CRMHosting/CheeseMakingBath/docs/images/2020-11-29_17-01-23.png

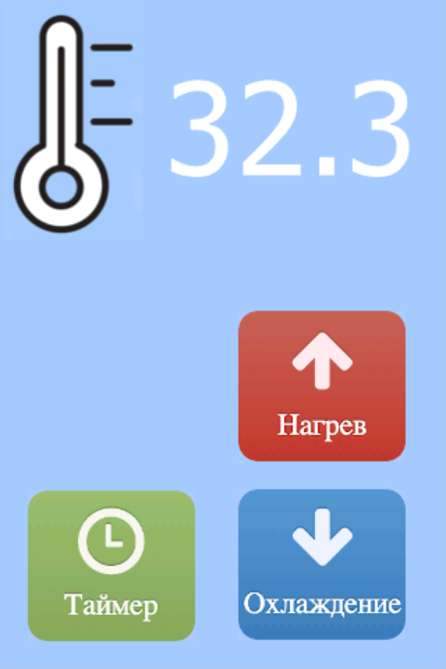
docs/images/2020-11-29_17-01-23.png
