CRMHosting/CheeseMakingBath/docs/images/2020-11-29_17-01-56.png

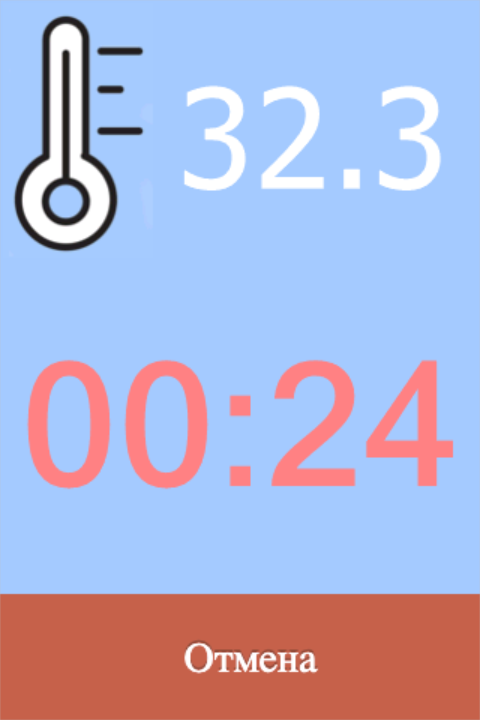
docs/images/2020-11-29_17-01-56.png
