CRMHosting/CheeseMakingBath/docs/images/2020-11-29_17-02-31.png

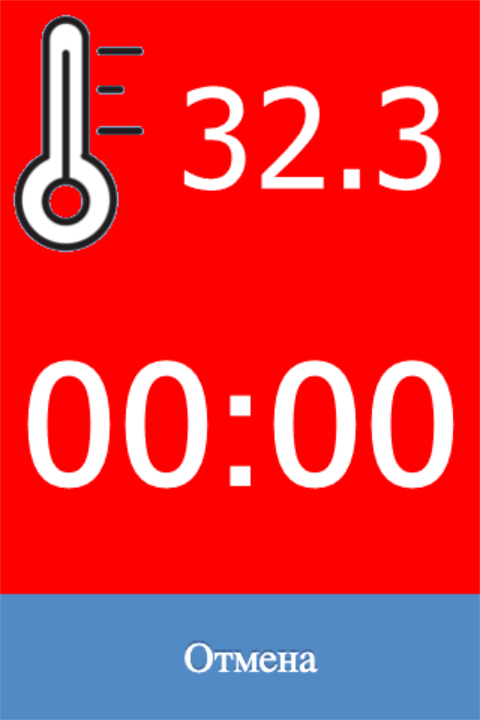
docs/images/2020-11-29_17-02-31.png
