CRMHosting/CheeseMakingBath/docs/images/2020-11-29_17-03-14.png

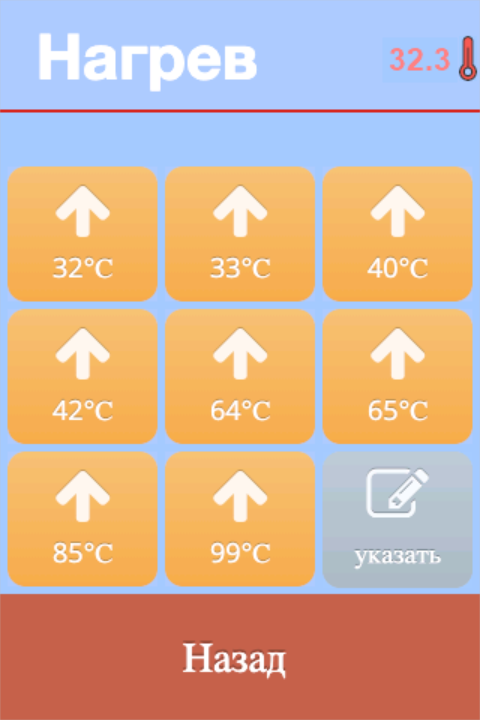
docs/images/2020-11-29_17-03-14.png
