CRMHosting/CheeseMakingBath/docs/images/2020-11-29_17-03-38.png

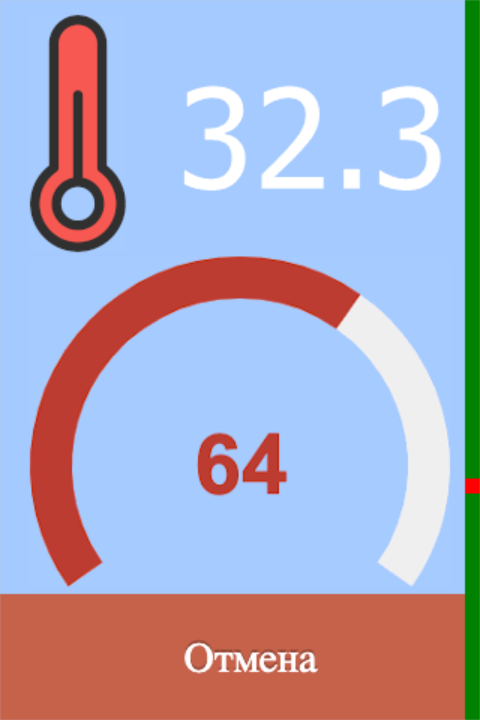
docs/images/2020-11-29_17-03-38.png
