CRMHosting/CheeseMakingBath/docs/images/2020-11-29_17-04-29.png

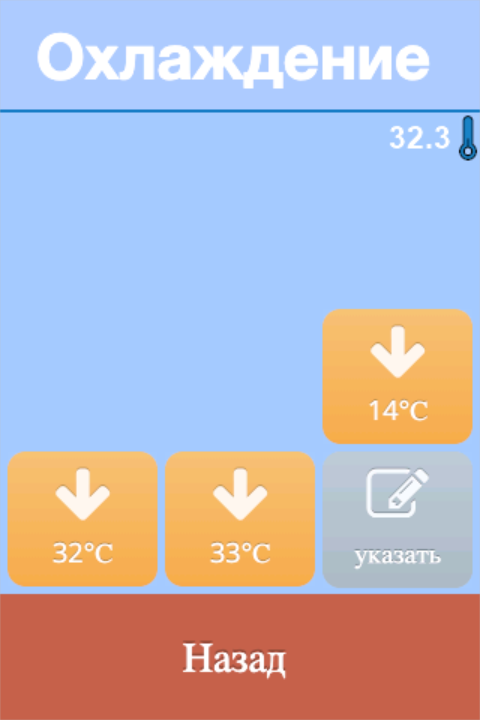
docs/images/2020-11-29_17-04-29.png
