CRMHosting/CheeseMakingBath/docs/images/2020-11-29_17-04-42.png

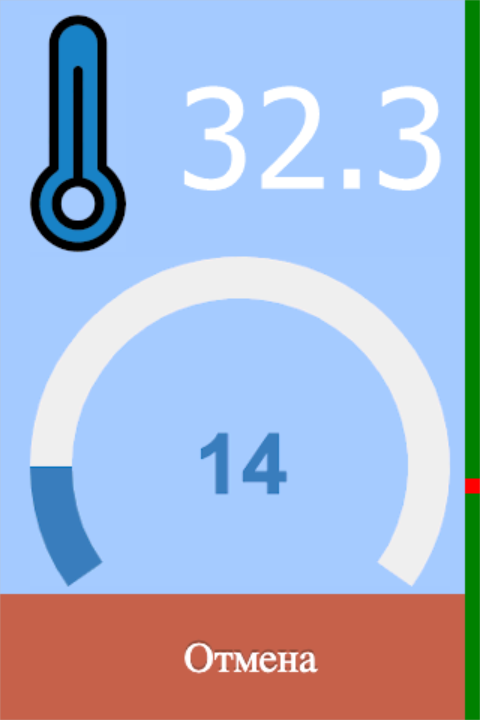
docs/images/2020-11-29_17-04-42.png
