CRMHosting/CheeseMakingBath/docs/images/2020-11-29_17-05-11.png

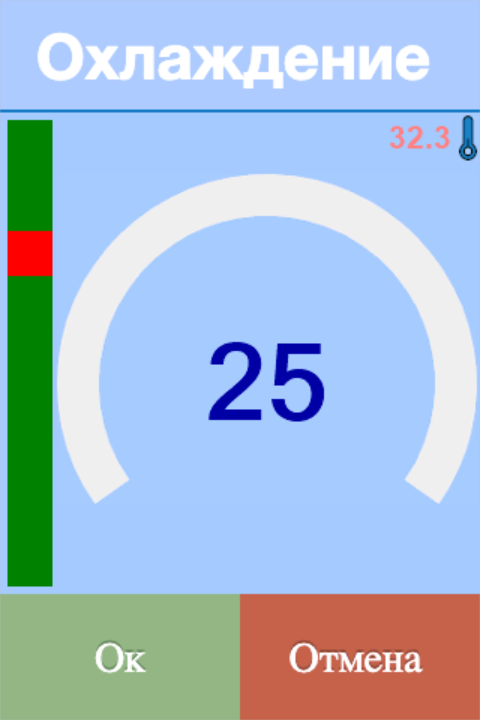
docs/images/2020-11-29_17-05-11.png
