CRMHosting/CheeseMakingBath/docs/images/2020-11-29_19-46-53.png

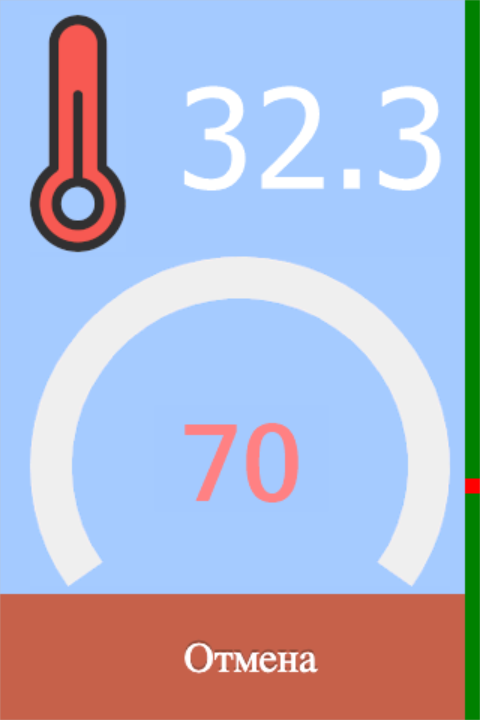
docs/images/2020-11-29_19-46-53.png
