CRMHosting/CheeseMakingBath/docs/images/1606628371465.jpg

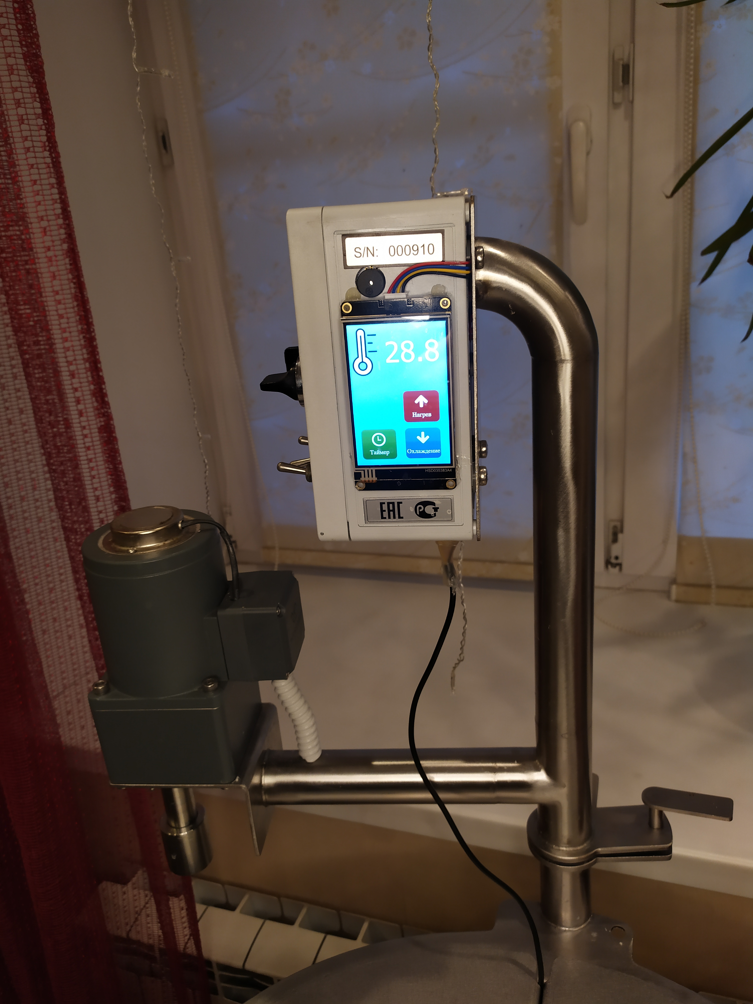
docs/images/1606628371465.jpg
