CRMHosting/CheeseMakingBath/docs/images/1606628371484.jpg

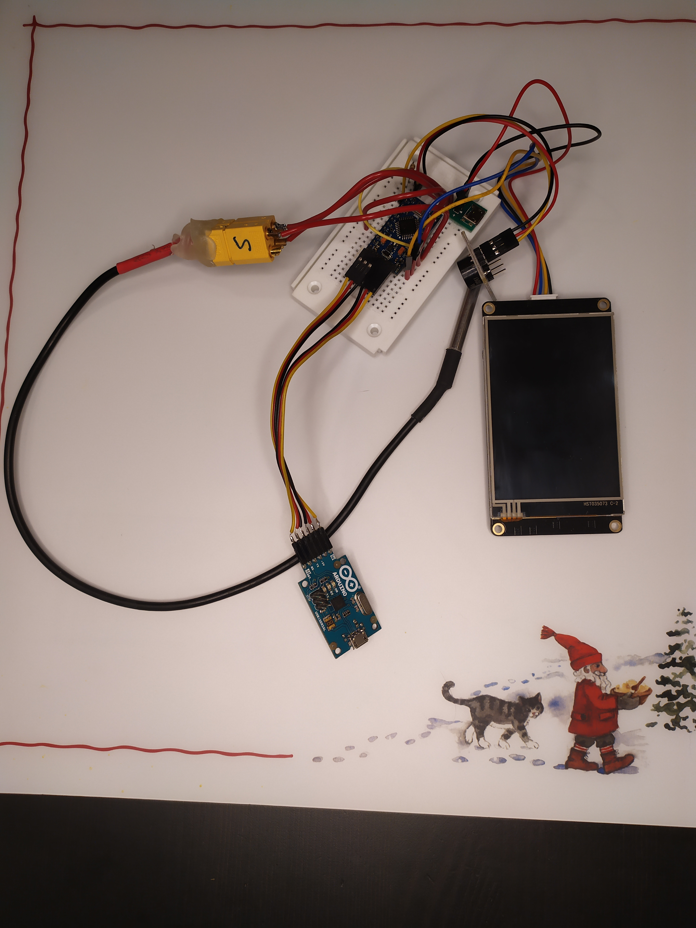
docs/images/1606628371484.jpg
