CRMHosting/CheeseMakingBath/docs/images/main-pH-280x420.png

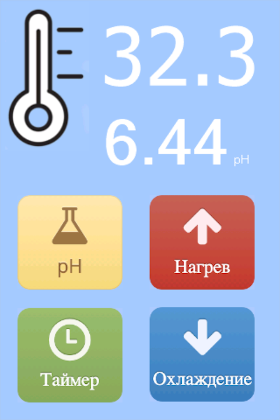
docs/images/main-pH-280x420.png
