CRMHosting/CheeseMakingBath/docs/images/pH-280x420.png

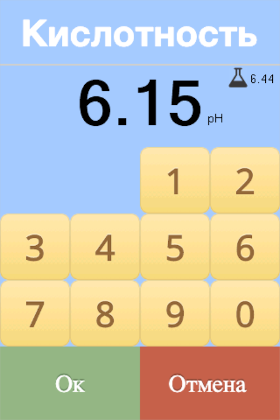
docs/images/pH-280x420.png
