CRMHosting/CheeseMakingBath/docs/images/pH-run-280x420.png

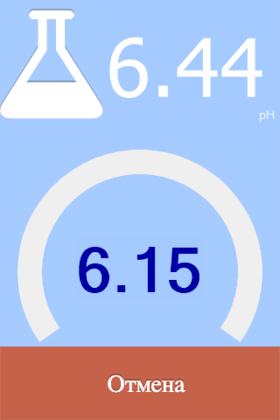
docs/images/pH-run-280x420.png
