CRMHosting/CheeseMakingBath/docs/images/screen-h-full-640x.png

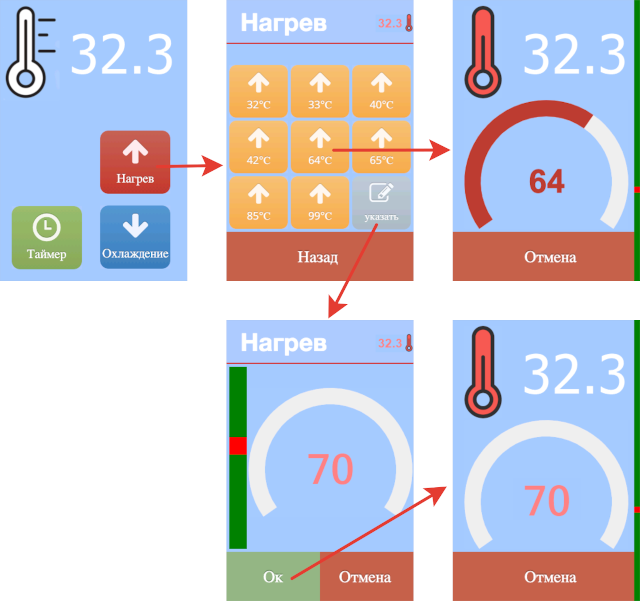
docs/images/screen-h-full-640x.png
