CRMHosting/CheeseMakingBath/docs/images/screen-pH.png

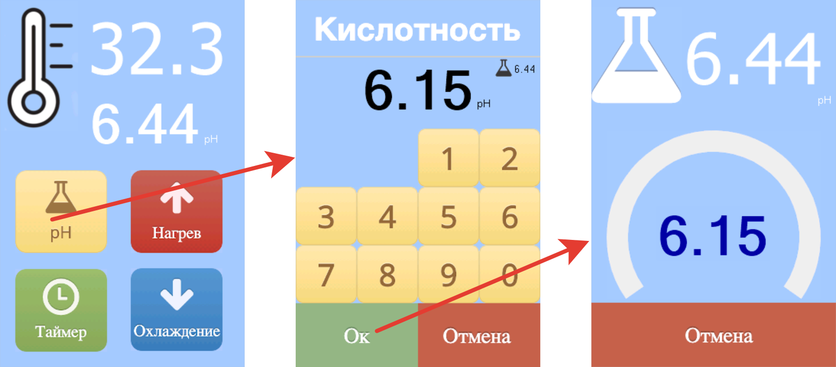
docs/images/screen-pH.png
