CRMHosting/CheeseMakingBath/Nextion/images/buttons/buttons-custom.png

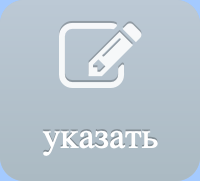
Nextion/images/buttons/buttons-custom.png
