CRMHosting/CheeseMakingBath/Nextion/images/buttons/cooling-buttons-14.png

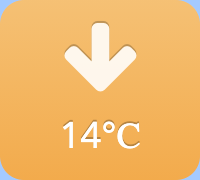
Nextion/images/buttons/cooling-buttons-14.png
