CRMHosting/CheeseMakingBath/Nextion/images/buttons/digital-button-0.png

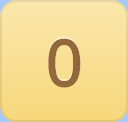
Nextion/images/buttons/digital-button-0.png
