CRMHosting/CheeseMakingBath/Nextion/images/buttons/digital-button-1.png

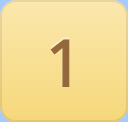
Nextion/images/buttons/digital-button-1.png
