CRMHosting/CheeseMakingBath/Nextion/images/buttons/heat-buttons-40.png

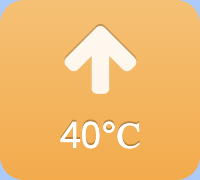
Nextion/images/buttons/heat-buttons-40.png
