CRMHosting/CheeseMakingBath/Nextion/images/buttons/heat-buttons-custom.png

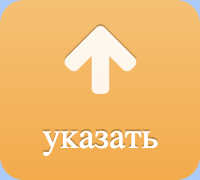
Nextion/images/buttons/heat-buttons-custom.png
