CRMHosting/CheeseMakingBath/Nextion/images/buttons/main-buttons-flocc.png

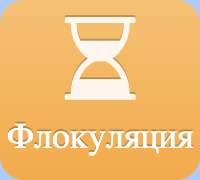
Nextion/images/buttons/main-buttons-flocc.png
