CRMHosting/CheeseMakingBath/Nextion/images/buttons/main-buttons-freese.png

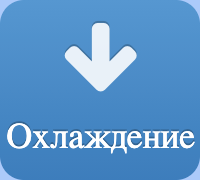
Nextion/images/buttons/main-buttons-freese.png
