CRMHosting/CheeseMakingBath/Nextion/images/buttons/main-buttons-heat.png

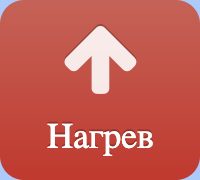
Nextion/images/buttons/main-buttons-heat.png
