CRMHosting/CheeseMakingBath/Nextion/images/buttons/main-buttons-pH.png

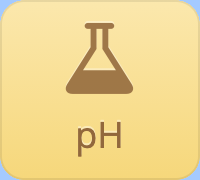
Nextion/images/buttons/main-buttons-pH.png
