CRMHosting/CheeseMakingBath/Nextion/images/buttons/main-buttons-timer.png

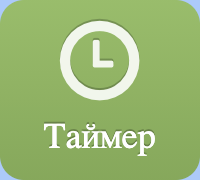
Nextion/images/buttons/main-buttons-timer.png
