CRMHosting/CheeseMakingBath/Nextion/images/buttons/timer-buttons-1h.png

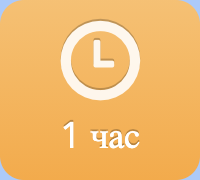
Nextion/images/buttons/timer-buttons-1h.png
