CRMHosting/CheeseMakingBath/Nextion/images/buttons/timer-buttons-30sec.png

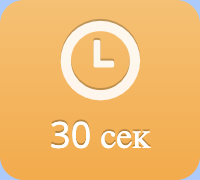
Nextion/images/buttons/timer-buttons-30sec.png
