CRMHosting/CheeseMakingBath/Nextion/images/other/2020-11-22_15-21-24.png

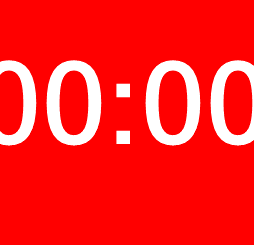
Nextion/images/other/2020-11-22_15-21-24.png
