CRMHosting/CheeseMakingBath/Nextion/images/other/2020-11-23_12-30-18.png

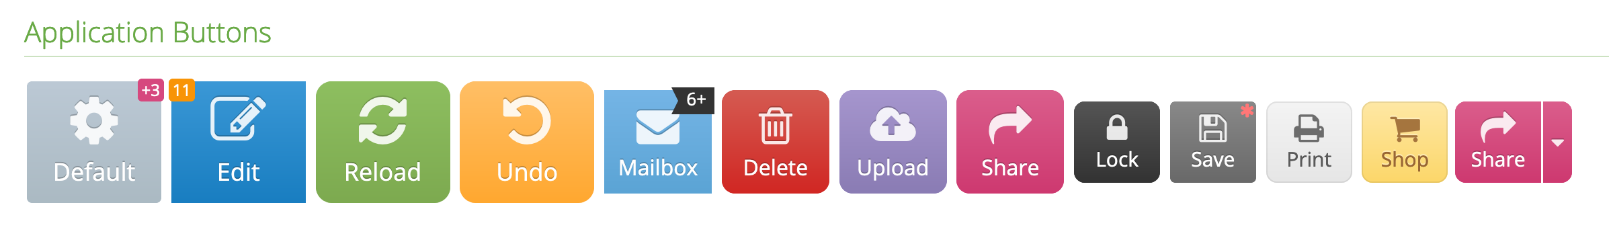
Nextion/images/other/2020-11-23_12-30-18.png
