CRMHosting/CheeseMakingBath/Nextion/images/other/2020-11-23_13-08-33.png

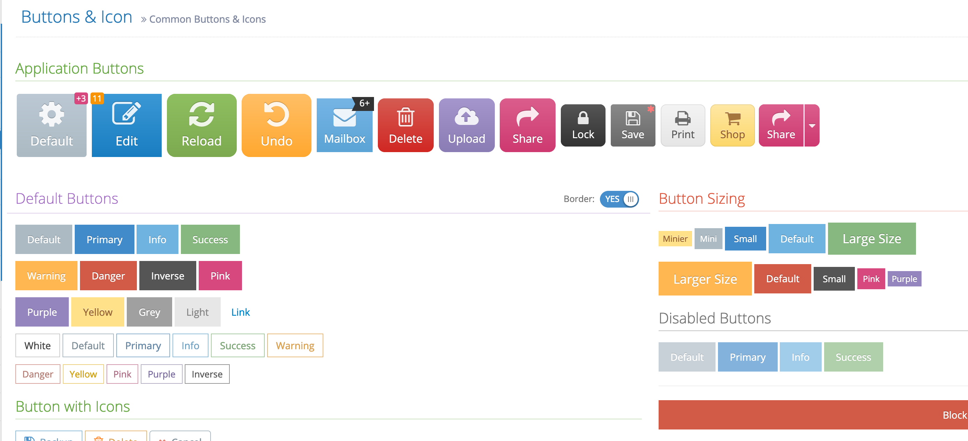
Nextion/images/other/2020-11-23_13-08-33.png
