CRMHosting/CheeseMakingBath/Nextion/images/other/chees_320_480.png

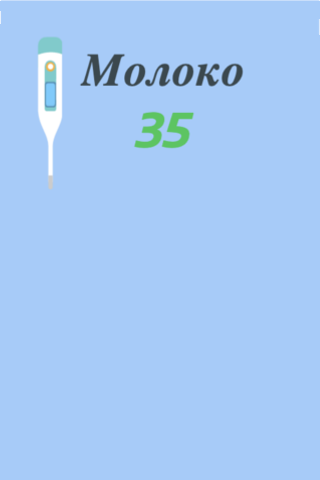
Nextion/images/other/chees_320_480.png
