CRMHosting/CheeseMakingBath/Nextion/images/other/timer_30min_1.jpg

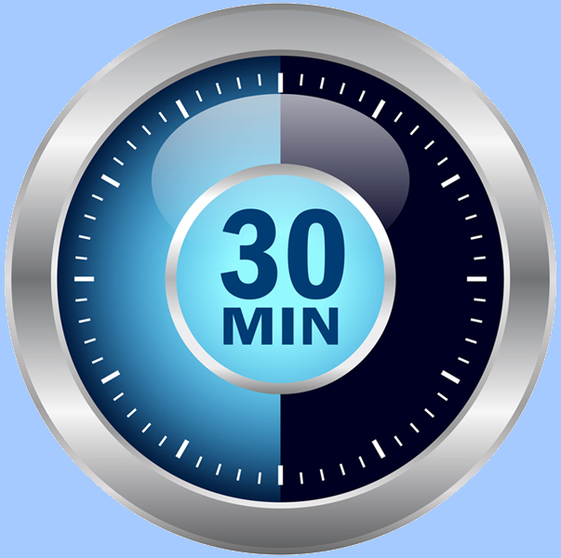
Nextion/images/other/timer_30min_1.jpg
