CRMHosting/CheeseMakingBath/Nextion/images/other/timer_button.jpg

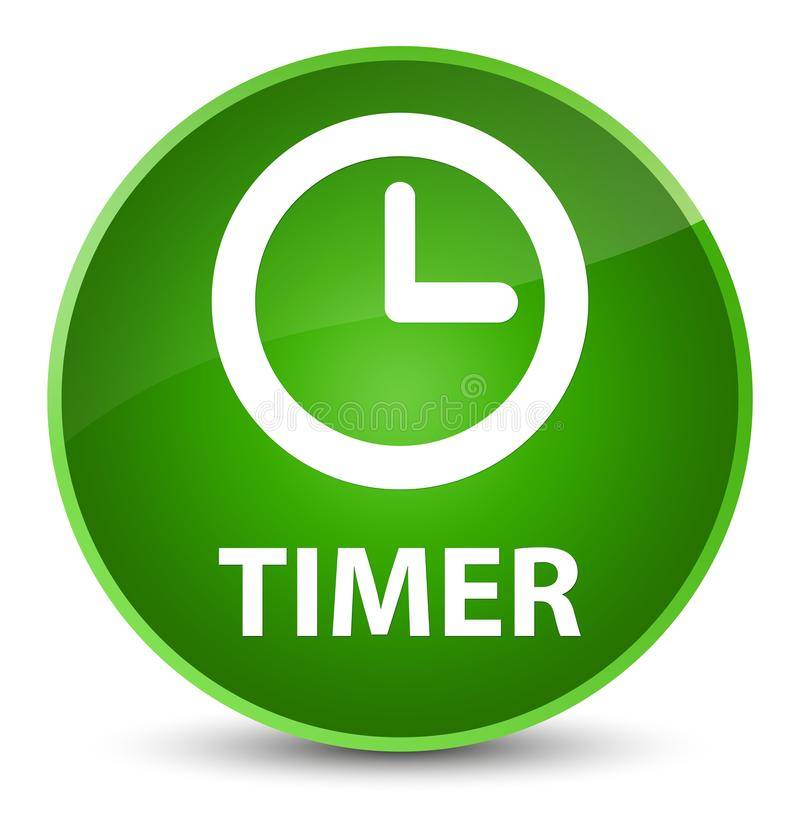
Nextion/images/other/timer_button.jpg
