CRMHosting/CheeseMakingBath/Nextion/images/other/timer_button_2.png

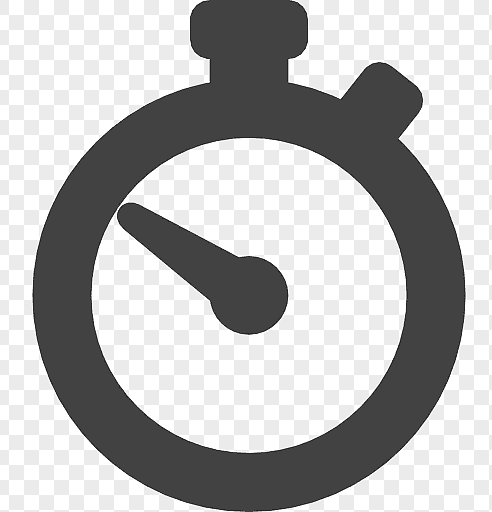
Nextion/images/other/timer_button_2.png
