CRMHosting/CheeseMakingBath/Nextion/images/temperature/arrow-down-blue.png

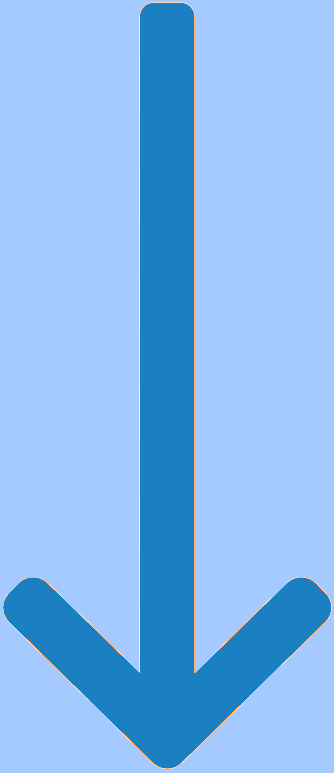
Nextion/images/temperature/arrow-down-blue.png
