CRMHosting/CheeseMakingBath/Nextion/images/temperature/arrow.png

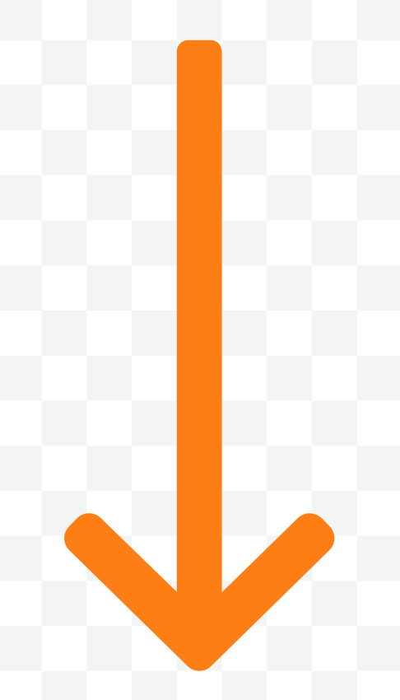
Nextion/images/temperature/arrow.png
